Rocketdude1984/MMIN-Converter/docs/Images/image2.jpg

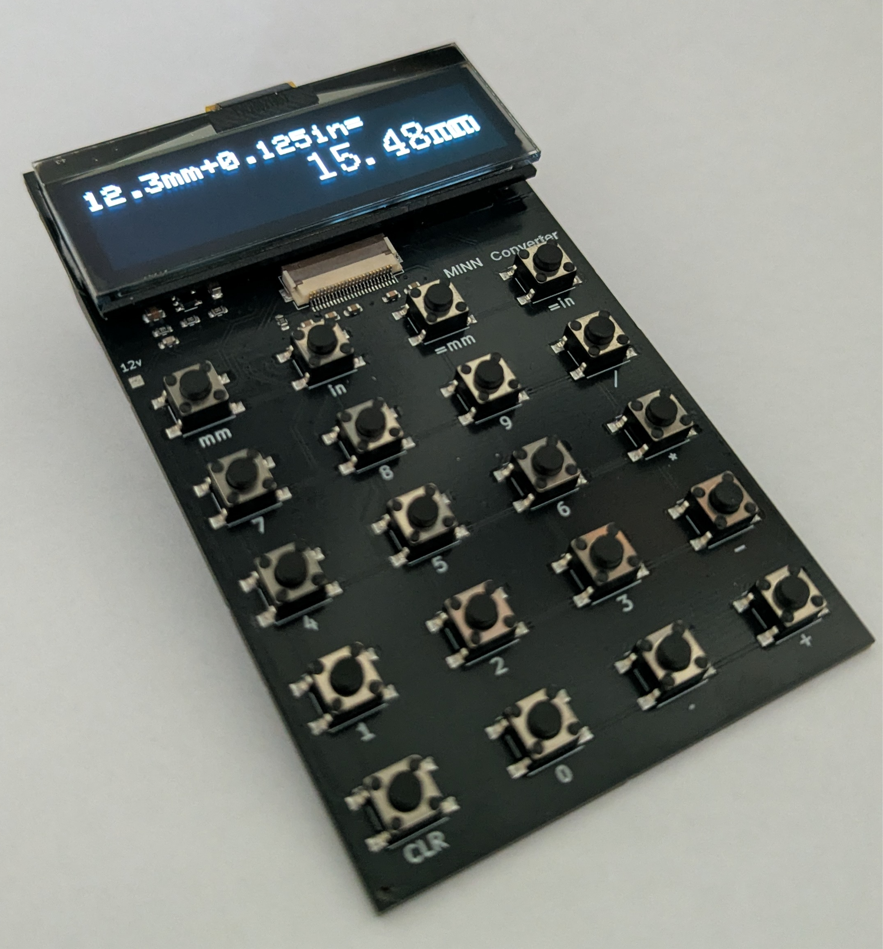
docs/Images/image2.jpg
